brainsmoke/esp32leddriver/pcb/driver_aluball_v1/alu_driver.png

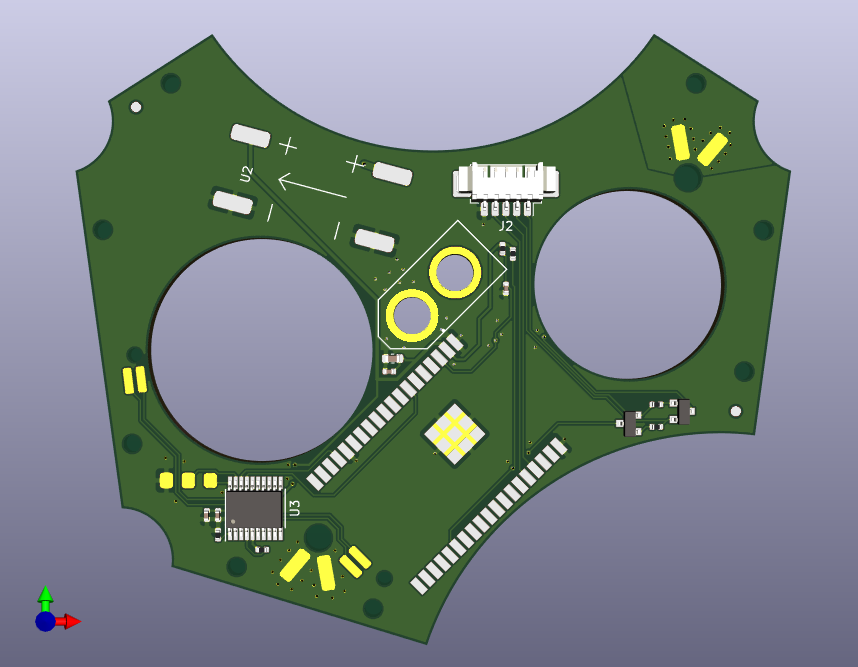
pcb/driver_aluball_v1/alu_driver.png
