brainsmoke/esp32leddriver/firmware/stm32/strip4/strip4.h

#ifndef STRIP4_H
#define STRIP4_H

/* configurable parameters (SRAM needed: more than 9*8*N_LEDS_PER_STRIP + 512 bytes) */

/* no bigger than 80x3 or 60x4 */
#ifndef N_VALUES_PER_LED
#define N_VALUES_PER_LED  (3)
#endif

#ifndef N_LEDS_PER_STRIP
#define N_LEDS_PER_STRIP (60)
#endif

/* static constants */

#define N_STRIPS (4) /* code changes needed to change this */

/* derived constants */

#define N_VALUES_PER_STRIP (N_LEDS_PER_STRIP*N_VALUES_PER_LED)
#define N_LEDS (N_LEDS_PER_STRIP*4)
#define N_VALUES (N_VALUES_PER_STRIP*4)
#define N_BYTES (N_VALUES*2)

#if N_VALUES_PER_STRIP > 240
#error "strips too long"
#endif

#ifndef __ASSEMBLER__

#include <stdint.h>

extern uint8_t remainders[N_VALUES];

void bitbang16(uint16_t *buf, volatile uint16_t *gpio_out);

#endif

#endif // STRIP4_H
