brainsmoke/esp32leddriver/firmware/stm32/common/ws2812_dma.c

/*
 * Copyright (c) 2023 Erik Bosman <erik@minemu.org>
 *
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
 * (http://opensource.org/licenses/mit-license.html)
 *
 */

#include <stdlib.h>
#include "stm32f0xx.h"

#include "ws2812_dma.h"

/* each timer channel/compare register is mapped onto one DMA channel by hardware  */

#define DMA_CHANNEL_DATA  (DMA1_Channel2)
#define DMA_CHANNEL_SET   (DMA1_Channel3)
#define DMA_CHANNEL_CLEAR (DMA1_Channel4)

#define TIMER_COMPARE_DATA  (TIM1->CCR1)
#define TIMER_COMPARE_SET   (TIM1->CCR2)
#define TIMER_COMPARE_CLEAR (TIM1->CCR4)
#define TIMER_PULSELEN      (TIM1->ARR)

	                                   /* v------- 16 bit ------v */
#define DMA_CONFIG_MEM_TO_PERIPH_16BIT ( (1*DMA_CCR_MSIZE_0) | (1*DMA_CCR_PSIZE_0) | \
                                         (1*DMA_CCR_DIR) | (2*DMA_CCR_PL_0) )

#define DMA_CONFIG_BUF_TO_PERIPH_16BIT ( DMA_CCR_MINC | DMA_CONFIG_MEM_TO_PERIPH_16BIT )

	                                  /* v------- 8 bit -------v */
#define DMA_CONFIG_MEM_TO_PERIPH_8BIT ( (0*DMA_CCR_MSIZE_0) | (0*DMA_CCR_PSIZE_0) | \
                                        (1*DMA_CCR_DIR) | (2*DMA_CCR_PL_0) )

#define DMA_CONFIG_BUF_TO_PERIPH_8BIT ( DMA_CCR_MINC | DMA_CONFIG_MEM_TO_PERIPH_8BIT )

#if DMA_WIDTH == 8
#define DMA_CONFIG_MEM_TO_PERIPH DMA_CONFIG_MEM_TO_PERIPH_8BIT
#define DMA_CONFIG_BUF_TO_PERIPH DMA_CONFIG_BUF_TO_PERIPH_8BIT
#elif DMA_WIDTH == 16
#define DMA_CONFIG_MEM_TO_PERIPH DMA_CONFIG_MEM_TO_PERIPH_16BIT
#define DMA_CONFIG_BUF_TO_PERIPH DMA_CONFIG_BUF_TO_PERIPH_16BIT
#endif

#define DMA_CONFIG_INTERRUPT_HALF_TRANSFER (DMA_CCR_HTIE)
#define DMA_CONFIG_INTERRUPT_FULL_TRANSFER (DMA_CCR_TCIE)

static transfer_t pin_mask;

static void ws2812_dma_setup(GPIO_TypeDef *gpio, transfer_t mask)
{
	pin_mask = mask;
	RCC->AHBENR |= RCC_AHBENR_DMA1EN;
	DMA_CHANNEL_SET->CPAR = (uint32_t)&gpio->BSRR;
	DMA_CHANNEL_SET->CMAR = (uint32_t)&pin_mask;
	DMA_CHANNEL_SET->CCR  = DMA_CONFIG_MEM_TO_PERIPH;

	DMA_CHANNEL_DATA->CPAR = (uint32_t)&gpio->BRR;
	//DMA_CHANNEL_DATA->CMAR = ...
	DMA_CHANNEL_DATA->CCR  = DMA_CONFIG_BUF_TO_PERIPH |
	                         DMA_CONFIG_INTERRUPT_HALF_TRANSFER;

	DMA_CHANNEL_CLEAR->CPAR = (uint32_t)&gpio->BRR;
	DMA_CHANNEL_CLEAR->CMAR = (uint32_t)&pin_mask;
	DMA_CHANNEL_CLEAR->CCR  = DMA_CONFIG_MEM_TO_PERIPH |
	                          DMA_CONFIG_INTERRUPT_FULL_TRANSFER;

	NVIC_EnableIRQ(DMA1_Channel2_3_IRQn);
	NVIC_SetPriority (DMA1_Channel2_3_IRQn, 1);
	NVIC_EnableIRQ(DMA1_Channel4_5_IRQn);
	NVIC_SetPriority (DMA1_Channel4_5_IRQn, 1);
}

void ws2812_dma_start(volatile transfer_t buf[], uint32_t n_transfers)
{
	/* clear flags, ... */

	DMA_CHANNEL_DATA->CMAR = (uint32_t)buf;
	DMA_CHANNEL_SET->CNDTR = n_transfers;
	DMA_CHANNEL_DATA->CNDTR = n_transfers;
	DMA_CHANNEL_CLEAR->CNDTR = n_transfers;

	DMA_CHANNEL_SET->CCR |= DMA_CCR_EN;
	DMA_CHANNEL_DATA->CCR |= DMA_CCR_EN;
	DMA_CHANNEL_CLEAR->CCR |= DMA_CCR_EN;

	/* start timer */
	TIM1->CR1 |= TIM_CR1_CEN;
}

static void ws2812_dma_stop(void)
{
	/* stop timer */
	TIM1->CR1 &= ~TIM_CR1_CEN;
	TIM1->DIER &=~ ( TIM_DIER_CC1DE | TIM_DIER_CC2DE | TIM_DIER_CC4DE );

	/* disable dma */
	DMA_CHANNEL_SET->CCR &=~ DMA_CCR_EN;
	DMA_CHANNEL_DATA->CCR &=~ DMA_CCR_EN;
	DMA_CHANNEL_CLEAR->CCR &=~ DMA_CCR_EN;

	TIM1->DIER |= ( TIM_DIER_CC1DE | TIM_DIER_CC2DE | TIM_DIER_CC4DE );

	TIM1->CNT = 0;
	TIM1->SR  = 0;
}

/* half-transfer */
void DMA1_Channel2_3_IRQHandler(void)
{
	__enable_irq();
	ws2812_half_transfer();
	DMA1->IFCR = DMA_ISR_HTIF2;
}

/* full-transfer */
void DMA1_Channel4_5_IRQHandler(void)
{
	ws2812_dma_stop();
	__enable_irq();
	ws2812_full_transfer();
	DMA1->IFCR = DMA_ISR_TCIF4;
}

static void ws2812_timer_setup(int t0h, int t1h, int t_pulse)
{
	RCC->APB2ENR |= RCC_APB2ENR_TIM1EN;

	TIM1->CR1 = (0*TIM_CR1_CKD_0) | /* no clock division */
	            (0*TIM_CR1_CMS_0) |
	            (0*TIM_CR1_DIR)   |
	            (0*TIM_CR1_OPM)   |
	            (0*TIM_CR1_URS)   |
	            (0*TIM_CR1_UDIS)  |
	            (0*TIM_CR1_CEN)   ; /* don't start counting yet */

//	TIM1->PSC = 0;

	TIM1->DIER = TIM_DIER_CC1DE | TIM_DIER_CC2DE | TIM_DIER_CC4DE;

	/* default */
//	TIM1->CCMR1 = (0*TIM_CCMR1_CC1S_0) | /* channel 1 = output compare */
//	              (0*TIM_CCMR1_CC2S_0) ; /* channel 2 = output compare */
//	TIM1->CCMR2 = (0*TIM_CCMR2_CC4S_0) ; /* channel 4 = output compare */

	TIMER_PULSELEN      = t_pulse - 1;

	TIMER_COMPARE_SET   = t_pulse - 1 - t1h;
	TIMER_COMPARE_DATA  = t_pulse - 1 + t0h - t1h;
	TIMER_COMPARE_CLEAR = t_pulse - 1;
}


void ws2812_dma_init(GPIO_TypeDef *gpio, transfer_t mask, int t0h, int t1h, int t_pulse)
{
	ws2812_dma_setup(gpio, mask);
	ws2812_timer_setup(t0h, t1h, t_pulse);
}
