brainsmoke/esp32leddriver/firmware/esp32/fs/csrf.py

import binascii, hashlib, os, re

import esphttpd

_host_random = None
def host_random():
    global _host_random
    if _host_random == None:
        _host_random = os.urandom(16)
    return _host_random

def invalidate_tokens():
    _host_random = None

# file.html?boot=<token>
# easy cache control
_boot_token = None
def get_boot_token():
    global _boot_token
    if _boot_token == None:
        _boot_token = os.urandom(16).hex()
    return _boot_token

# Generating tokens

def generate_csrf_cookie():
    return os.urandom(16)

def generate_csrf_token( req, cookie ):
    hash_ = hashlib.sha256( cookie )
    hash_.update( req.get_remote_host() )
    hash_.update( host_random() )
    return binascii.b2a_base64(hash_.digest())[:24]

# Getting/setting cookies

def set_csrf_cookie( req, cookie ):
    secure = b''
    if req.get_protocol() == 'https':
        secure = b'; Secure'
    req.add_header( b'Set-Cookie', b'csrf=' + binascii.hexlify(cookie) + secure + b'; SameSite=Lax; HttpOnly' )

def get_csrf_cookie( req ): # not very pretty
    cookie_header = req.get_header(b'Cookie')
    ix = 0
    while True:

        ix = cookie_header.find(b'csrf=', ix)
        if ix == -1:
            return None

        if ix == 0 or cookie_header[ix-1] in b'; ':
            hexcookie = cookie_header[ix+5:ix+37]
            break

        ix += 5

    if len(hexcookie) != 32:
        return None

    try:
        return binascii.unhexlify(hexcookie)
    except ValueError:
        return None

# Interface

def verify_csrf_token( req, token ):
    d = esphttpd.session_dict( req )
    sess_token = d.get( 'csrf_token', None ) # token present in current session (= tcp connection)
    if sess_token != None and token == sess_token:
        return True

    cookie = get_csrf_cookie( req )
    if cookie == None:
        return False
    token_from_cookie = generate_csrf_token( req, cookie )

    if token == token_from_cookie:
        d['csrf_token'] = token_from_cookie
        return True

    return False

def get_csrf_token( req ):
    d = esphttpd.session_dict( req )
    token = d.get( 'csrf_token', None )
    if token != None:
        return token

    cookie = get_csrf_cookie( req )
    if cookie == None:
        cookie = generate_csrf_cookie()
        set_csrf_cookie( req, cookie )

    token = generate_csrf_token( req, cookie )
    d['csrf_token'] = token
    return token

# X-API-Key

def verify_api_key( req, key ):
    return key != None and req.get_header(b'X-API-Key') == key.encode('utf-8')
